Chrismettal/PedalDev/img/404/nice_tiny.jpg

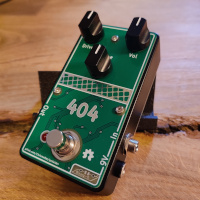
img/404/nice_tiny.jpg
